Sarix1/picclock/src/timer.h

#ifndef TIMER_H
#define	TIMER_H

#include "global.h"

#define TIMER0_RESET_VALUE 6
#define TIMER1_RESET_VALUE 57344

void startTimer0();
void startTimer1();
void startTimer2();

//void stopTimer0();
//void stopTimer1();
void stopTimer2();

#endif	/* TIMER_H */
