Sarix1/picclock/src/notes.h

// notes
#define NOTE_B0  3
#define NOTE_C1  3
#define NOTE_CS1 3
#define NOTE_D1  3
#define NOTE_DS1 3
#define NOTE_E1  4
#define NOTE_F1  4
#define NOTE_FS1 4
#define NOTE_G1  4
#define NOTE_GS1 5
#define NOTE_A1  5
#define NOTE_AS1 5
#define NOTE_B1  6
#define NOTE_C2  6
#define NOTE_CS2 6
#define NOTE_D2  7
#define NOTE_DS2 7
#define NOTE_E2  8
#define NOTE_F2  8
#define NOTE_FS2 9
#define NOTE_G2  9
#define NOTE_GS2 10
#define NOTE_A2  11
#define NOTE_AS2 11
#define NOTE_B2  12
#define NOTE_C3  13
#define NOTE_CS3 13
#define NOTE_D3  14
#define NOTE_DS3 15
#define NOTE_E3  16
#define NOTE_F3  17
#define NOTE_FS3 18
#define NOTE_G3  19
#define NOTE_GS3 20
#define NOTE_A3  22
#define NOTE_AS3 23
#define NOTE_B3  24
#define NOTE_C4  26
#define NOTE_CS4 27
#define NOTE_D4  29
#define NOTE_DS4 31
#define NOTE_E4  33
#define NOTE_F4  34
#define NOTE_FS4 37
#define NOTE_G4  39
#define NOTE_GS4 41
#define NOTE_A4  44
#define NOTE_AS4 46
#define NOTE_B4  49
#define NOTE_C5  52
#define NOTE_CS5 55
#define NOTE_D5  58
#define NOTE_DS5 62
#define NOTE_E5  65
#define NOTE_F5  69
#define NOTE_FS5 74
#define NOTE_G5  78
#define NOTE_GS5 83
#define NOTE_A5  88
#define NOTE_AS5 93
#define NOTE_B5  98
#define NOTE_C6  104
#define NOTE_CS6 110
#define NOTE_D6  117
#define NOTE_DS6 124
#define NOTE_E6  131
#define NOTE_F6  139
#define NOTE_FS6 148
#define NOTE_G6  156
#define NOTE_GS6 166
#define NOTE_A6  176
#define NOTE_AS6 186
#define NOTE_B6  197
#define NOTE_C7  209
#define NOTE_CS7 221
#define NOTE_D7  234
#define NOTE_DS7 248
#define NOTE_E7  263
#define NOTE_F7  279
#define NOTE_FS7 296
#define NOTE_G7  313
#define NOTE_GS7 332
#define NOTE_A7  352
#define NOTE_AS7 372
#define NOTE_B7  395
#define NOTE_C8  418
#define NOTE_CS8 443
#define NOTE_D8  469
#define NOTE_DS8 497
